TuDo-Makerspace/Smart-Mandolyn-RC-710/images/App.jpg

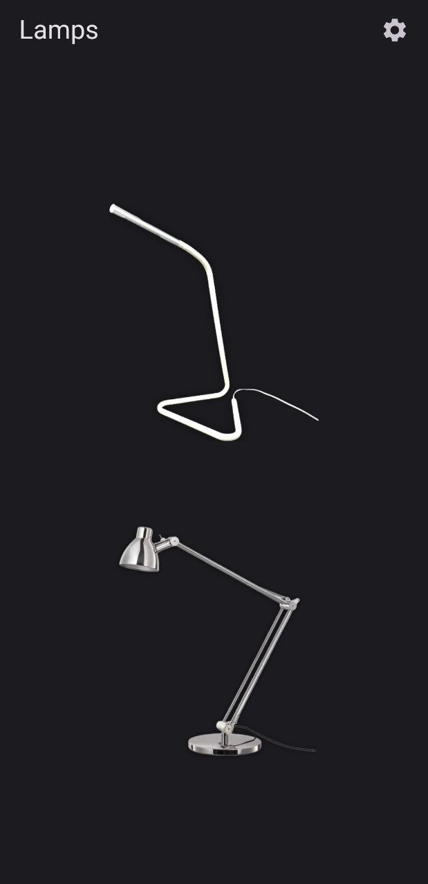
images/App.jpg
