TuDo-Makerspace/Smart-Mandolyn-RC-710/RC-710/Schematic-Modified/Schematic.kicad_sch

## KiCad design RC-710/Schematic-Modified/Schematic.kicad_sch (2025-05-17, an earlier design)

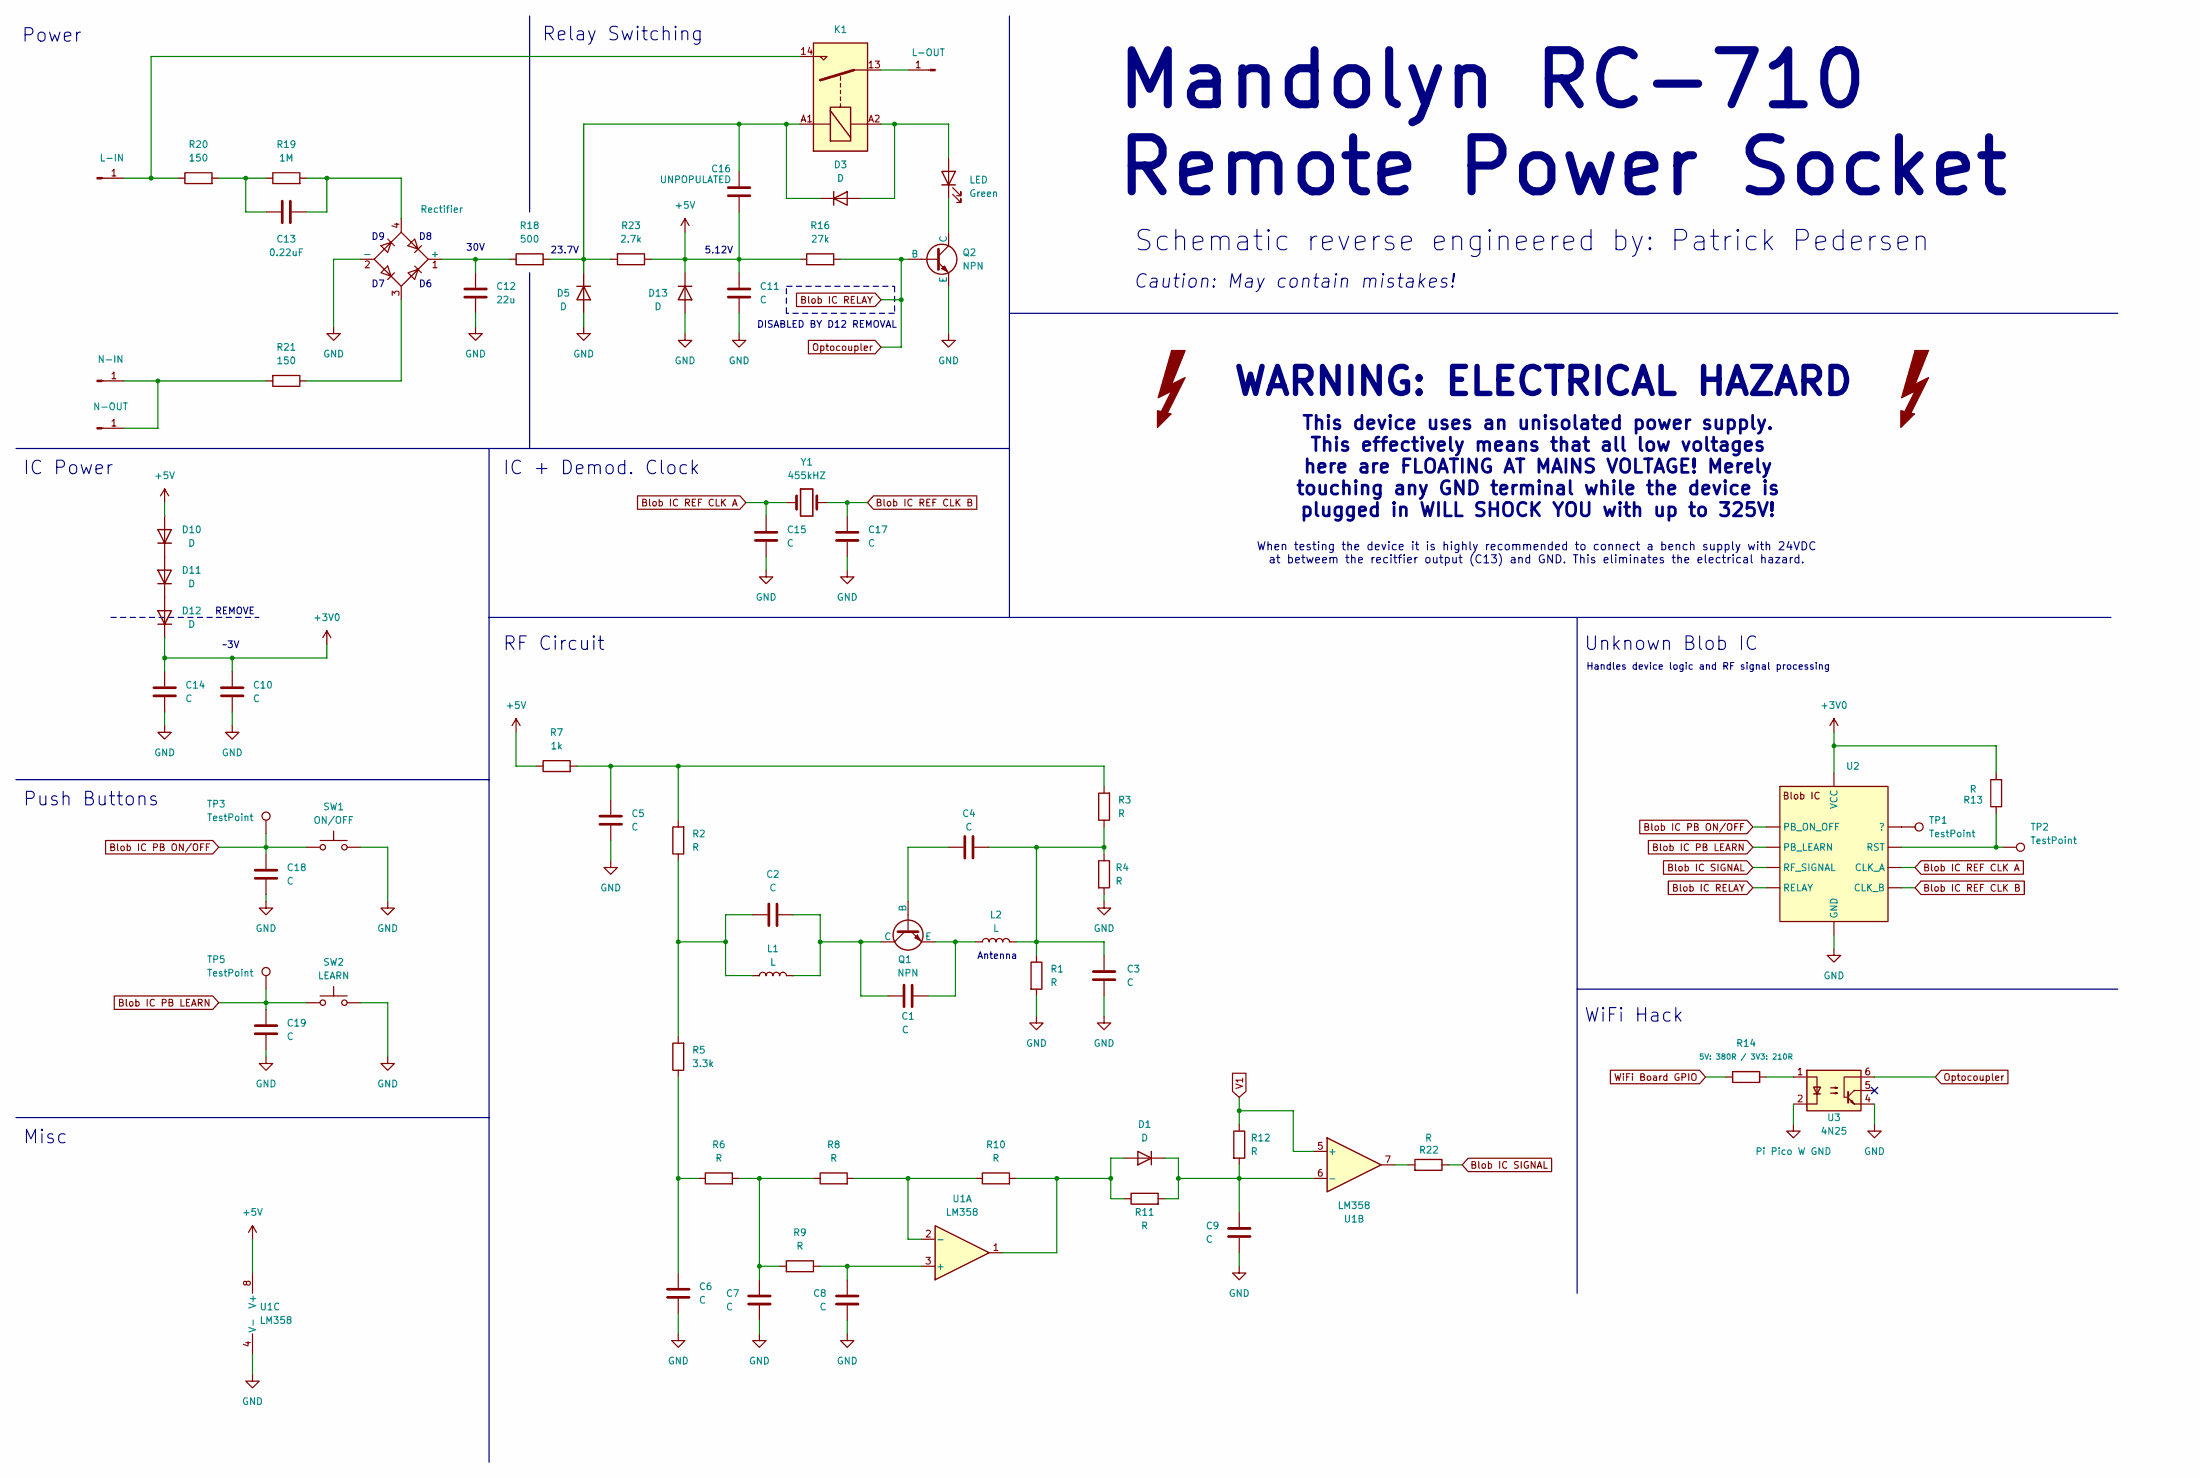
[picture p28: schematic Schematic.kicad_sch]

Parts:
C1, C2, C3, C4, C5, C6, C7, C8, C9, C10, C11, C14, C15, C17, C18, C19: C
C12: 22u
C13: 0.22uF
C16: UNPOPULATED
D1, D3, D5, D10, D11, D12, D13: D
K1: Fujitsu_FTR-LYAA005x; Relay_SPST-NO_Fujitsu_FTR-LYAA005x_FormA_Vertical
L1, L2: L
L-IN: Pad
L-OUT: Pad
LED: Green
N-IN: Pad
N-OUT: Pad
Q1, Q2: NPN
R1, R2, R3, R4, R6, R8, R9, R10, R11, R12, R13, R22: R
R5: 3.3k
R7: 1k
R14: 5V: 380R / 3V3: 210R
R16: 27k
R18: 500
R19: 1M
R20, R21: 150
R23: 2.7k
Rectifier: Diode_Bridge_Diotec_ABS
SW1: ON/OFF
SW2: LEARN
TP1, TP2, TP3, TP5: TestPoint
U1: LM358
U2: (no value)
U3: 4N25; DIP-6_W7.62mm
Y1: 455kHZ

Connections:
+3V0: C10.1, C14.1, D12.1 (K), R13.2, U2.
+5V: C11.1, C16.2, D10.2 (A), D13.1 (K), R7.1, R16.1, R23.1, U1.8 (V+)
Blob IC PB LEARN: C19.1, SW2.1, TP5.1, U2.
Blob IC PB ON/OFF: C18.1, SW1.1, TP3.1, U2.
Blob IC REF CLK A: C15.1, U2., Y1.1
Blob IC REF CLK B: C17.1, U2., Y1.2
Blob IC RELAY: Q2.2 (B), R16.2, U2., U3.6
Blob IC SIGNAL: R22.1, U2.
GND: C3.2, C5.2, C6.2, C7.2, C8.2, C9.2, C10.2, C11.2, C12.2, C14.2, C15.2, C17.2, C18.2, C19.2, D5.2 (A), D13.2 (A), Q2.3 (E), R1.2, R4.2, Rectifier.2 (-), SW1.2, SW2.2, U1.4 (V-), U2., U3.4
unnamed: C1.1, C2.2, L1.2, Q1.1 (C)
unnamed: C1.2, L2.1, Q1.3 (E)
unnamed: C2.1, L1.1, R2.1, R5.2
unnamed: C3.1, C4.1, L2.2, R1.1, R3.1, R4.1
unnamed: C4.2, Q1.2 (B)
unnamed: C5.1, R2.2, R3.2, R7.2
unnamed: C6.1, R5.1, R6.1
unnamed: C7.1, R6.2, R8.1, R9.2
unnamed: C8.1, R9.1, U1.3 (+)
unnamed: C9.1, D1.1 (K), R11.2, R12.2, U1.6 (-)
unnamed: C12.1, R18.1, Rectifier.1 (+)
unnamed: C13.1, R19.1, R20.2
unnamed: C13.2, R19.2, Rectifier.4
unnamed: C16.1, D3.1 (K), D5.1 (K), K1.A1, R18.2, R23.2
unnamed: D1.2 (A), R10.2, R11.1, U1.1
unnamed: D3.2 (A), K1.A2, LED.2 (A)
unnamed: D10.1 (K), D11.2 (A)
unnamed: D11.1 (K), D12.2 (A)
unnamed: K1.13, L-OUT.1
unnamed: K1.14, L-IN.1, R20.1
unnamed: LED.1 (K), Q2.1 (C)
unnamed: N-IN.1, N-OUT.1, R21.2
unnamed: R8.2, R10.1, U1.2 (-)
unnamed: R13.1, TP2.1, U2.
unnamed: R14.2, U3.1
unnamed: R21.1, Rectifier.3
unnamed: R22.2, U1.7
unnamed: TP1.1, U2.
Pi Pico W GND: U3.2
V1: R12.1, U1.5 (+)
WiFi Board GPIO: R14.1

Notes on the sheet:
Relay Switching
23.7V
This device uses an unisolated power supply. This effectively means that all low voltages here are FLOATING AT MAINS VOLTAGE! Merely touching any GND terminal while the device is plugged in WILL SHOCK YOU with up to 325V!
Schematic reverse engineered by: Patrick Pedersen
Misc
Mandolyn RC-710 Remote Power Socket
30V
Unknown Blob IC
IC Power
Antenna
Caution: May contain mistakes!
DISABLED BY D12 REMOVAL
When testing the device it is highly recommended to connect a bench supply with 24VDC at betweem the recitfier output (C13) and GND. This eliminates the electrical hazard.
REMOVE
WARNING: ELECTRICAL HAZARD
WiFi Hack
IC + Demod. Clock
~3V
Push Buttons
RF Circuit
5.12V
Handles device logic and RF signal processing
Power
